Chiptune-Anamnesis/YM2149F-Pi3/src/settings.h

#pragma once
#include <Arduino.h>
#include "config.h"

// ============================================================================
// SETTINGS MODULE
// Per-chip and global configuration with pot mapping
// ============================================================================

// --- Target Selection ---
enum SettingsTarget {
  TARGET_ALL = 0,
  TARGET_CHIP0,
  TARGET_CHIP1,
  TARGET_CHIP2,
  TARGET_V1,
  TARGET_V2,
  TARGET_V3,
  TARGET_V4,
  TARGET_V5,
  TARGET_V6,
  TARGET_V7,
  TARGET_V8,
  TARGET_V9,
  TARGET_COUNT
};

// --- Pot Parameter Categories ---
// Organize 50+ parameters into logical groups for easy navigation
enum PotCategory : uint8_t {
  PCAT_OFF = 0,        // Disabled
  PCAT_VOICE,          // Detune, Octave, MaxVol, NoiseFreq, PortaSpeed
  PCAT_VIBRATO,        // VibRate, VibDepth, VibDelay
  PCAT_ENVELOPE,       // Attack, Decay, Sustain
  PCAT_TREMOLO,        // TremRate, TremDepth
  PCAT_PITCH_ENV,      // PitchAmt, PitchTime, PitchDir
  PCAT_SID,            // SidWave, SidDuty, SidDetune
  PCAT_FX_ECHO,        // EchoDelay, EchoRepeats, EchoDecay, EchoVol
  PCAT_FX_ARP,         // ArpSpeed, ArpPattern, ArpVol, ArpOctave
  PCAT_FX_CRUSH,       // Bits, Rate, Volume
  PCAT_FX_REVERB,      // Taps, Spacing, Decay, Detune, Vol
  PCAT_FX_CHORUS,      // Detune1, Detune2, Volume
  PCAT_SAMPLE,         // Select, Mode, Volume
  PCAT_GLOBAL,         // Expression, PolyMode
  PCAT_COUNT
};

// Parameter counts per category
#define PCAT_VOICE_PARAMS 5
#define PCAT_VIBRATO_PARAMS 3
#define PCAT_ENVELOPE_PARAMS 4
#define PCAT_TREMOLO_PARAMS 2
#define PCAT_PITCH_ENV_PARAMS 3
#define PCAT_SID_PARAMS 6
#define PCAT_FX_ECHO_PARAMS 4
#define PCAT_FX_ARP_PARAMS 4
#define PCAT_FX_CRUSH_PARAMS 3
#define PCAT_FX_REVERB_PARAMS 5
#define PCAT_FX_CHORUS_PARAMS 4
#define PCAT_SAMPLE_PARAMS 6
#define PCAT_GLOBAL_PARAMS 2

// Target value for "no targeting" (global/FX params)
#define TARGET_NONE 0xFF

// Full pot assignment (4 bytes per pot)
struct PotAssignment {
  PotCategory category;   // Which category
  uint8_t paramIndex;     // Which param within category (0-based)
  uint8_t target;         // TARGET_ALL..TARGET_V9, or TARGET_NONE for FX
  uint8_t reserved;       // Future use (curve type, etc)
};

// --- Per-Voice Settings ---
struct VoiceSettings {
  int8_t detuneCents;     // -50 to +50 cents
  int8_t octaveShift;     // -3 to +3 octaves
  uint8_t vibOn;          // 0=off, 1-127=intensity (bypasses mod wheel)
  uint8_t vibRateTenths;  // 10-150 (1.0-15.0 Hz in tenths)
  uint8_t vibDepthCents;  // 0-200 cents (2 semitones max)
  uint8_t vibDelay;       // 0-255 delay before vibrato starts (x10ms = 0-2550ms)
  uint8_t noiseFreq;      // 0-31 noise frequency (per-chip, voice 0 controls)
  uint8_t envAttack;      // 0-127 attack time
  uint8_t envDecay;       // 0-127 decay time
  uint8_t envSustain;     // 0-127 sustain level
  uint8_t sidPwmRate;     // 0-127 PWM sweep LFO rate (was sidOn)
  uint8_t sidWave;        // 0=square, 3=pulse (saw/triangle disabled)
  uint8_t sidDuty;        // 0-15 duty cycle (0=6%, 8=50%, 15=94%)
  uint8_t maxVolume;      // 0-15, caps voice output volume
  uint8_t portaOn;        // 0=off, 1=on (enables portamento/glide)
  uint8_t portaSpeed;     // 0-127 glide speed (0=slow, 127=fast)
  // Tremolo (volume LFO)
  uint8_t tremoloOn;      // 0=off, 1-127=intensity
  uint8_t tremoloRate;    // 10-150 (1.0-15.0 Hz in tenths)
  uint8_t tremoloDepth;   // 0-100 (percentage of volume swing)
  // Pitch envelope
  uint8_t pitchEnvAmt;    // 0-24 semitones
  uint8_t pitchEnvTime;   // 0-127 time (speed of sweep)
  uint8_t pitchEnvDir;    // 0=down (start high), 1=up (start low)
  // SID extended params
  uint8_t sidPwmDepth;    // 0-15 how much duty varies during PWM sweep
  uint8_t sidSync;        // 0=off, 1-3=sync to voice A/B/C within chip
  uint8_t sidRing;        // 0=off, 1-3=ring mod with voice A/B/C within chip
  uint8_t sidNoise;       // 0=off, 1=on (mix YM noise into this voice)
  uint8_t envRelease;     // 0-127 release time
};

// --- Global Settings State ---
extern VoiceSettings voiceSettings[9];
extern SettingsTarget currentTarget;
extern PotAssignment potAssignments[3];  // 3 pots with flexible category/param/target

// --- Chip Link Settings ---
// When enabled, all 3 voices on a chip play the same note (with individual settings)
extern bool chipLink[3];

// Global link mode: 0=OFF, 1=CH1, 2=CH2, 3=ALL (CH1+CH2)
// When linked, chips inherit settings from Chip 0
extern uint8_t linkMode;
#define LINK_OFF  0
#define LINK_CH1  1
#define LINK_CH2  2
#define LINK_ALL  3

// Voice link mask: which Chip 0 voices participate in linking
// Bits 0,1,2 = voices A,B,C (default 0b111 = all linked)
extern uint8_t voiceLinkMask;
#define VOICE_LINK_A  0x01
#define VOICE_LINK_B  0x02
#define VOICE_LINK_C  0x04
#define VOICE_LINK_ALL 0x07

// --- Pot Reading State ---
extern int potValues[3];       // Current pot ADC values (smoothed)
extern int potLastValues[3];   // Last values for change detection

// --- MIDI Channel Settings ---
// 0-15 for channels 1-16, 0xFE = OFF (disabled), 0xFF = OMNI (all channels)
#define MIDI_CHANNEL_OFF  0xFE
#define MIDI_CHANNEL_OMNI 0xFF
// Note: volatile required because these are modified by Core 1 (display) and read by Core 0 (MIDI)
extern volatile uint8_t midiSynthChannel;   // MIDI channel for active mode (default: OMNI)

// --- MIDI Channel Routing ---
// Remaps incoming MIDI channels to internal channels before routing decisions.
// midiChannelRemap[X] = Y means incoming channel X is treated as internal channel Y.
// Default: identity mapping (0→0, 1→1, ..., 15→15)
// Use 0xFF to indicate "no remap" (pass through as-is)
#define MIDI_REMAP_NONE 0xFF
extern volatile uint8_t midiChannelRemap[16];

// --- USB Mode Setting ---
// 0 = USB-MIDI (default), 1 = USB-Serial (debug/YMPlayer)
// Takes effect on reboot
#define USB_MODE_MIDI   0
#define USB_MODE_SERIAL 1
extern uint8_t usbMode;

// --- Device Mode (YM / SID / SMPL) ---
// Only one mode active at a time
extern volatile bool sidModeGlobal;    // SID emulator mode (chips 1+2)
extern volatile bool sampleModeGlobal; // Sample playback mode (chip 2, 3 voices)
extern uint8_t sidDutyChip[2];  // Per-chip duty cycle: [0]=chip1, [1]=chip2 (0-15)

// --- Per-Sample Pitch + Length ---
// Each of the 64 samples (24 drums + 24 oneshots + 16 digi) has independent settings
#define TOTAL_SAMPLE_COUNT 64
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
